Mbutton-umich/FlexGlO/PCB/FlexGlO/Fancy_back.png

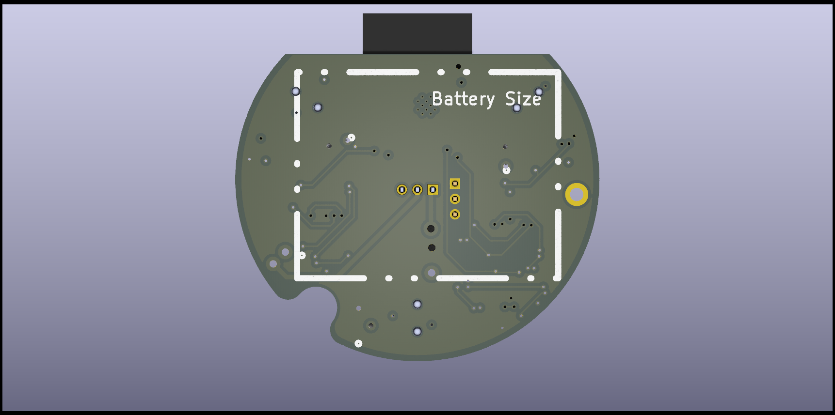
PCB/FlexGlO/Fancy_back.png
