Mbutton-umich/FlexGlO/PCB/FlexGlO/Fancy_close.png

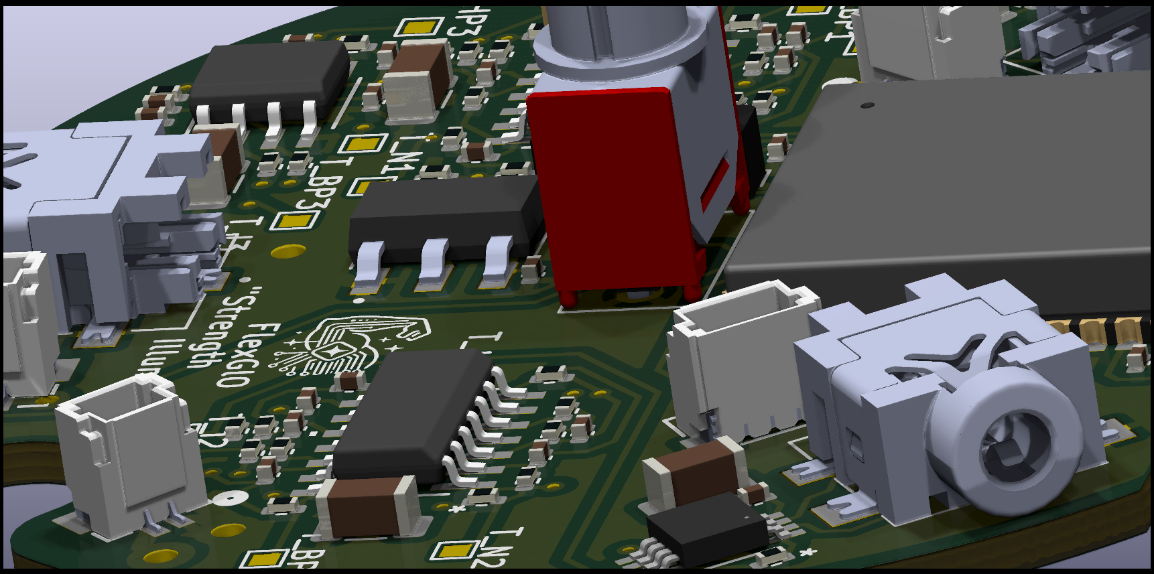
PCB/FlexGlO/Fancy_close.png
