Mbutton-umich/FlexGlO/PCB/FlexGlO/Fancy_side.png

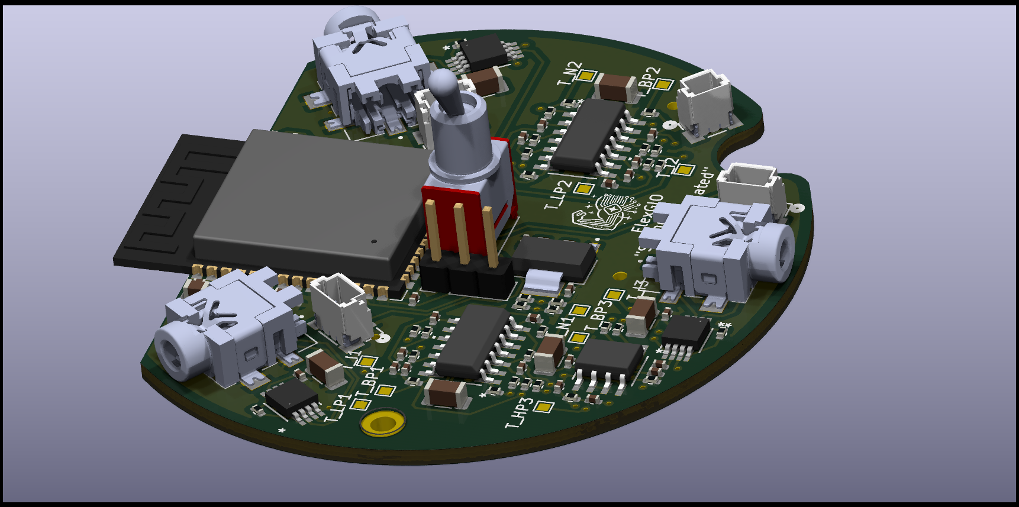
PCB/FlexGlO/Fancy_side.png
