Mbutton-umich/FlexGlO/PCB/FlexGlO/fancy_top.png

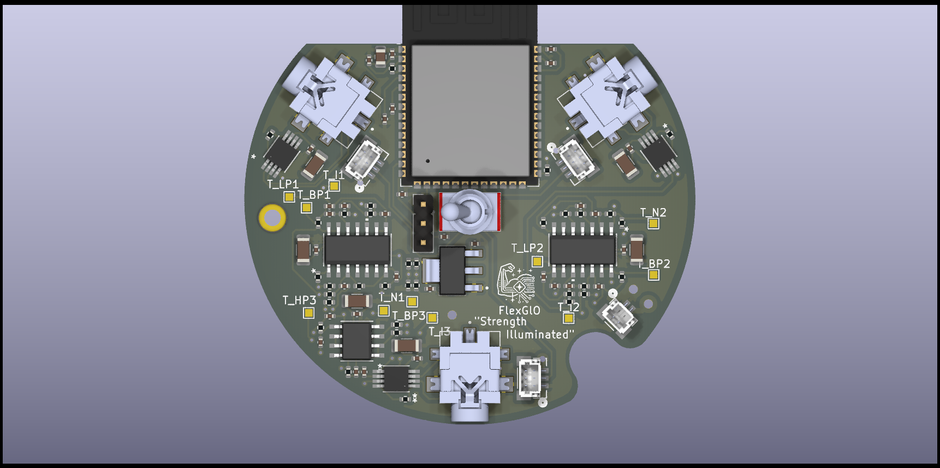
PCB/FlexGlO/fancy_top.png
