Mbutton-umich/FlexGlO/PCB/FlexGlO/grid_front.png

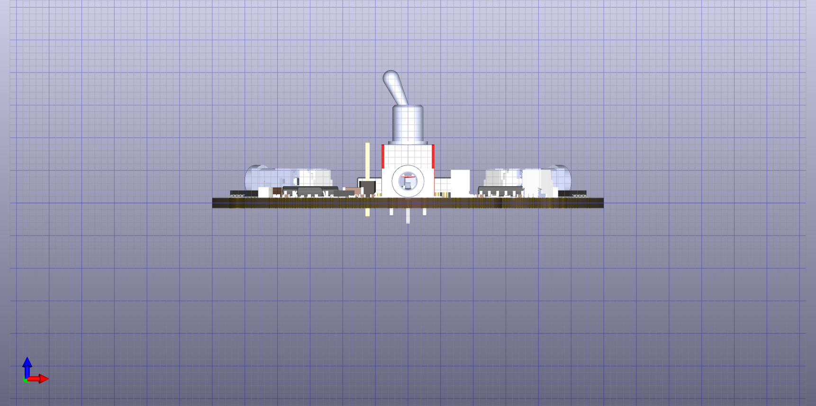
PCB/FlexGlO/grid_front.png
