Mbutton-umich/FlexGlO/PCB/FlexGlO/FlexParts/Footprints/CONN_BM02B-SRSS-TB_JST.STEP

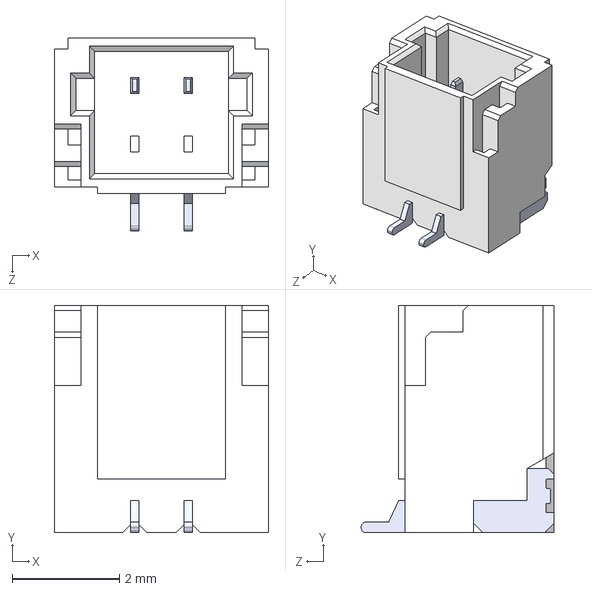
[picture p41: CAD file, 2024-12-03]
PCB/FlexGlO/FlexParts/Footprints/CONN_BM02B-SRSS-TB_JST.STEP
4.00 x 4.25 x 3.60 mm
