Mbutton-umich/FlexGlO/PCB/FlexGlO/FlexParts/Footprints/RC0402N_YAG.step

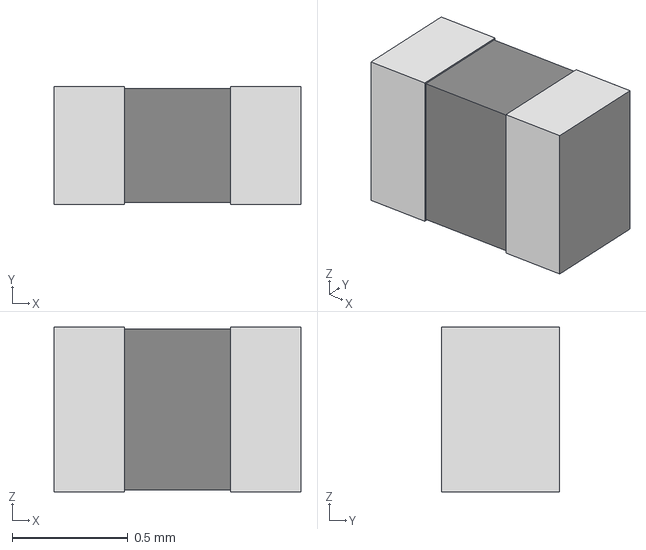
[picture p42: CAD file, 2024-12-03]
PCB/FlexGlO/FlexParts/Footprints/RC0402N_YAG.step
1.07 x 0.508 x 0.711 mm
