Mbutton-umich/FlexGlO/PCB/FlexGlO/FlexParts/Footprints/SW_PMS9P1B10M2QE.stp

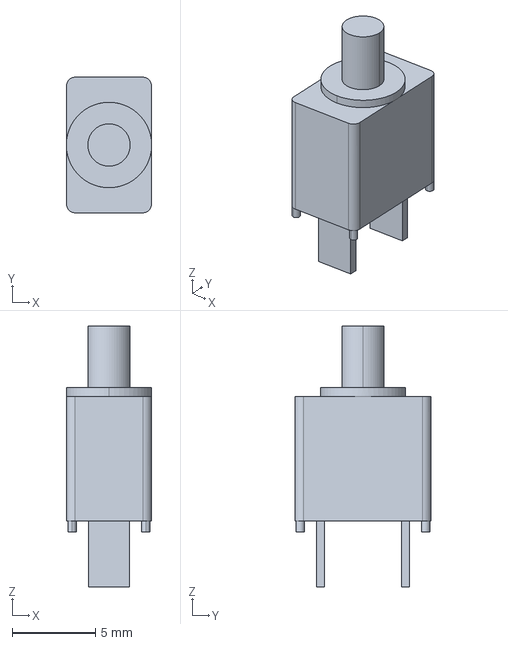
[picture p43: CAD file, 2024-12-03]
PCB/FlexGlO/FlexParts/Footprints/SW_PMS9P1B10M2QE.stp
5.12 x 8.13 x 15.6 mm
